majabojarska/just-rack/images/render/bottom.jpg

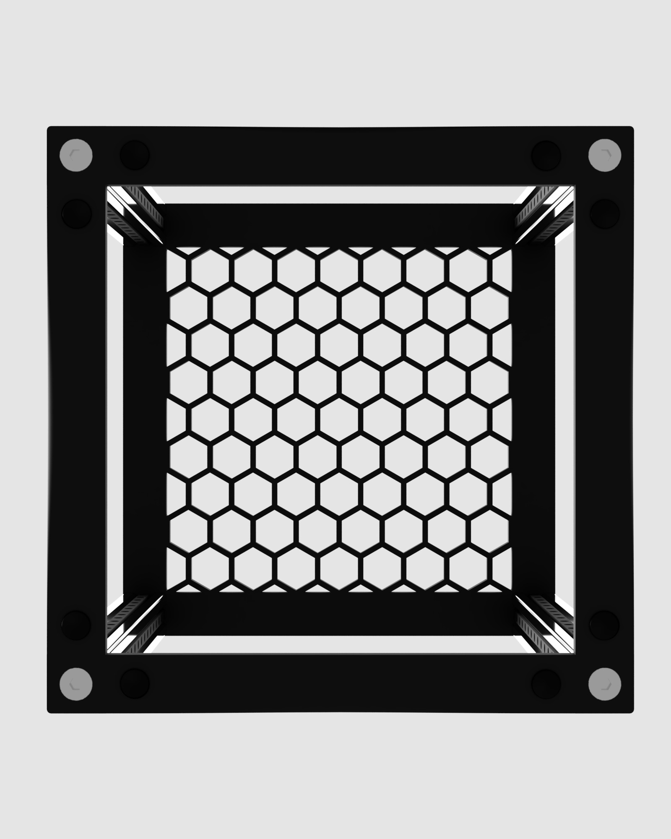
images/render/bottom.jpg
