majabojarska/just-rack/images/render/bottom_corner.jpg

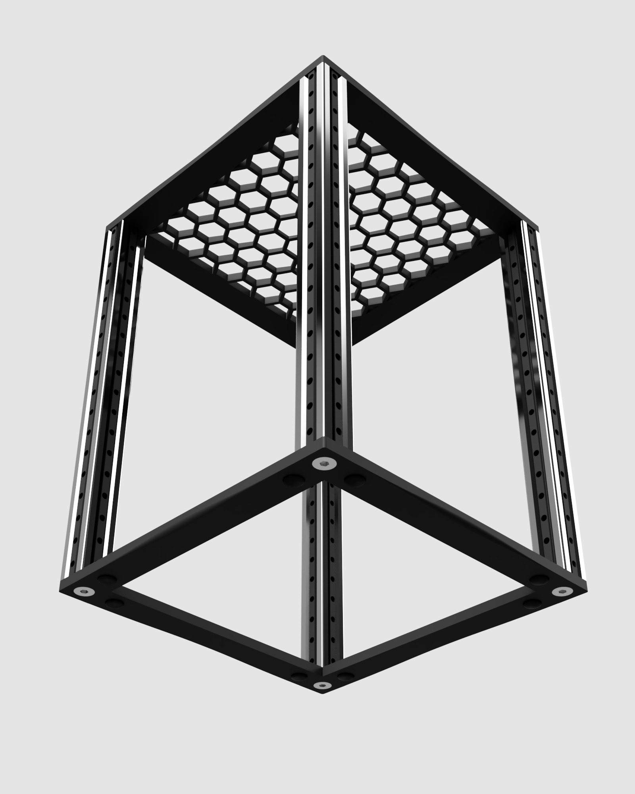
images/render/bottom_corner.jpg
