majabojarska/just-rack/images/render/frame_bottom.jpg

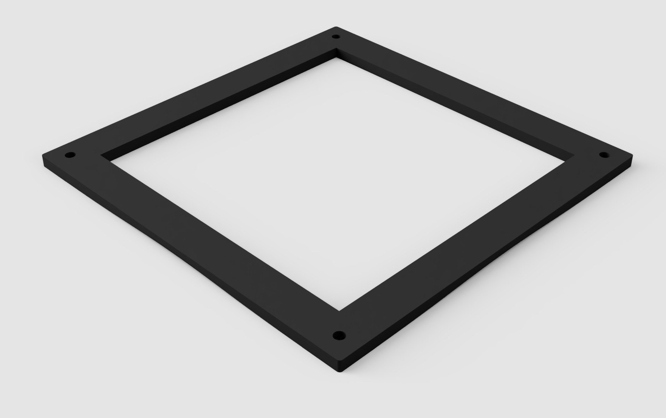
images/render/frame_bottom.jpg
