majabojarska/just-rack/images/render/frame_top.jpg

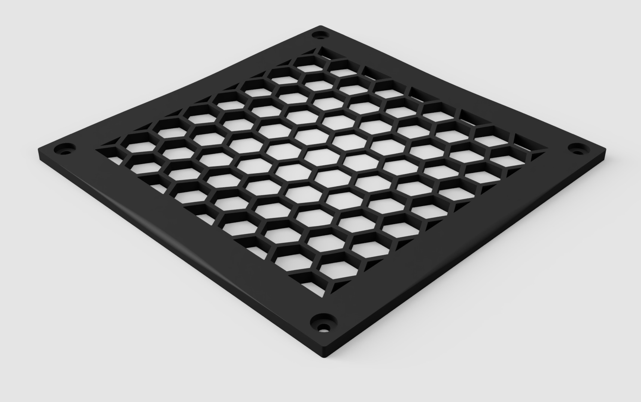
images/render/frame_top.jpg
