majabojarska/just-rack/images/render/front.jpg

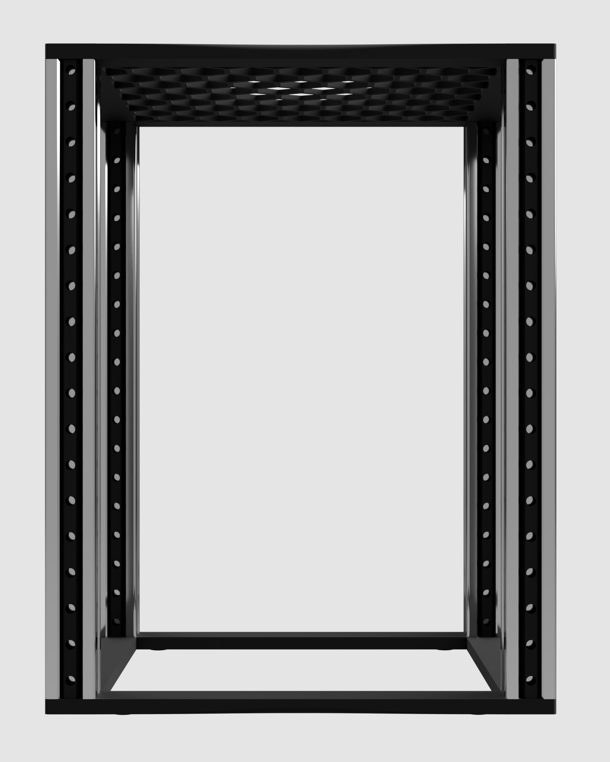
images/render/front.jpg
