majabojarska/just-rack/images/render/top.jpg

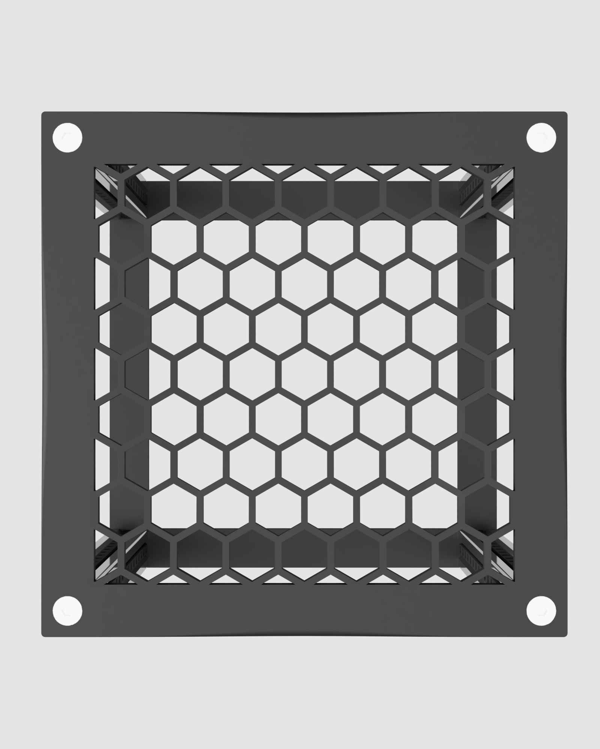
images/render/top.jpg
