majabojarska/just-rack/modules/lanberg_dsp1-1008/images/back_top.jpg

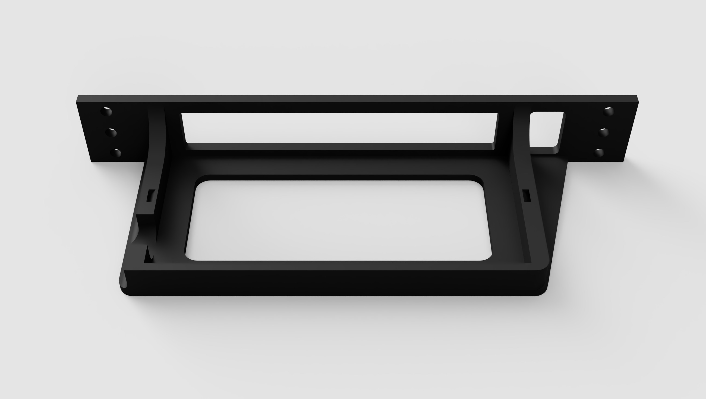
modules/lanberg_dsp1-1008/images/back_top.jpg
