majabojarska/just-rack/modules/lanberg_dsp1-1008/images/front.jpg

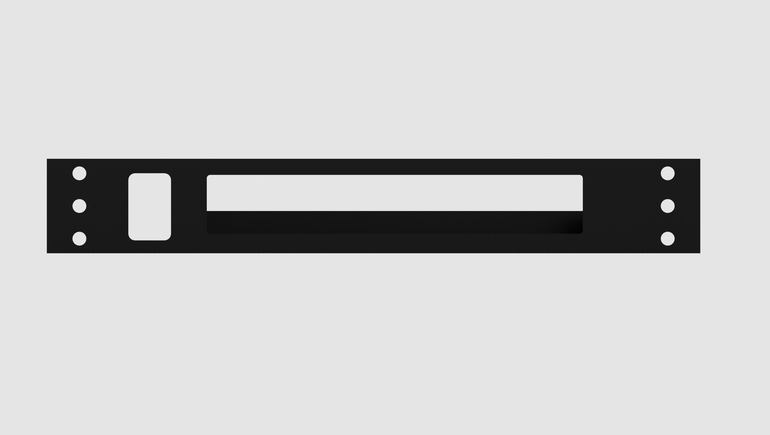
modules/lanberg_dsp1-1008/images/front.jpg
