majabojarska/just-rack/modules/ports_usb_hub/images/back.jpg

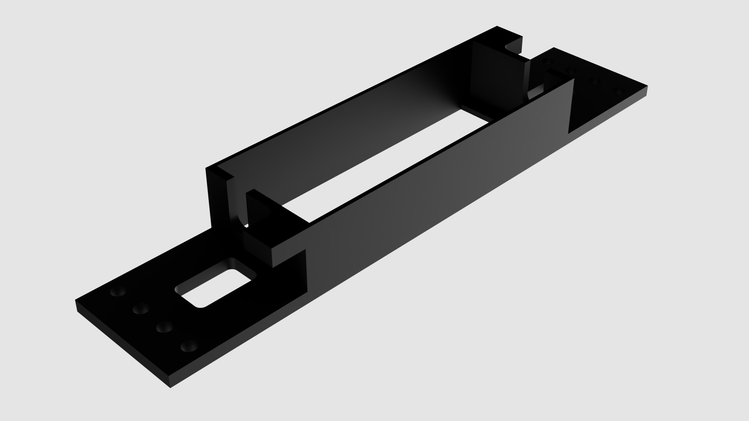
modules/ports_usb_hub/images/back.jpg
