majabojarska/just-rack/modules/ports_usb_hub/images/cover_back.jpg

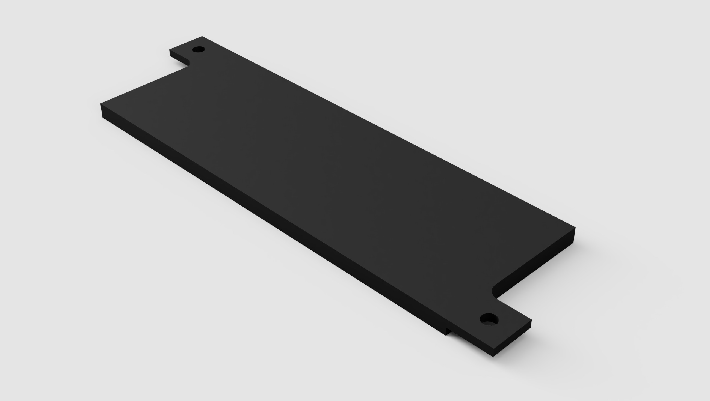
modules/ports_usb_hub/images/cover_back.jpg
