majabojarska/just-rack/modules/rpi3b_server/images/top_front.jpg

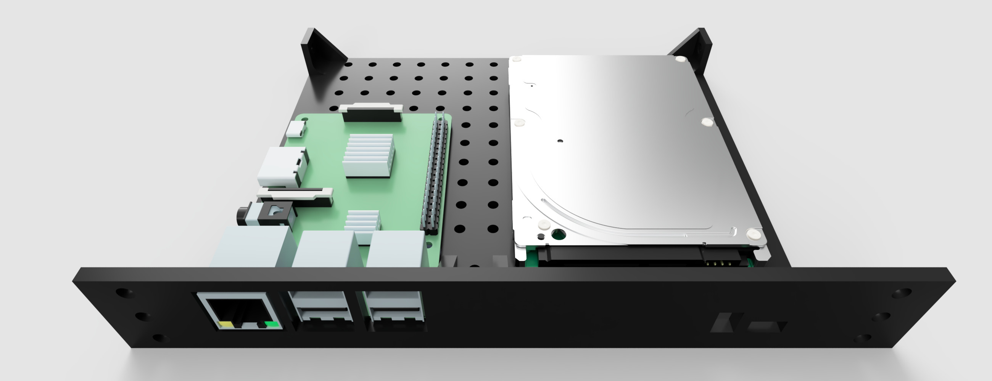
modules/rpi3b_server/images/top_front.jpg
